ThatAquarel/protovolt/hardware/mini/interface.kicad_sch

## KiCad design hardware/mini/interface.kicad_sch (2025-06-21)

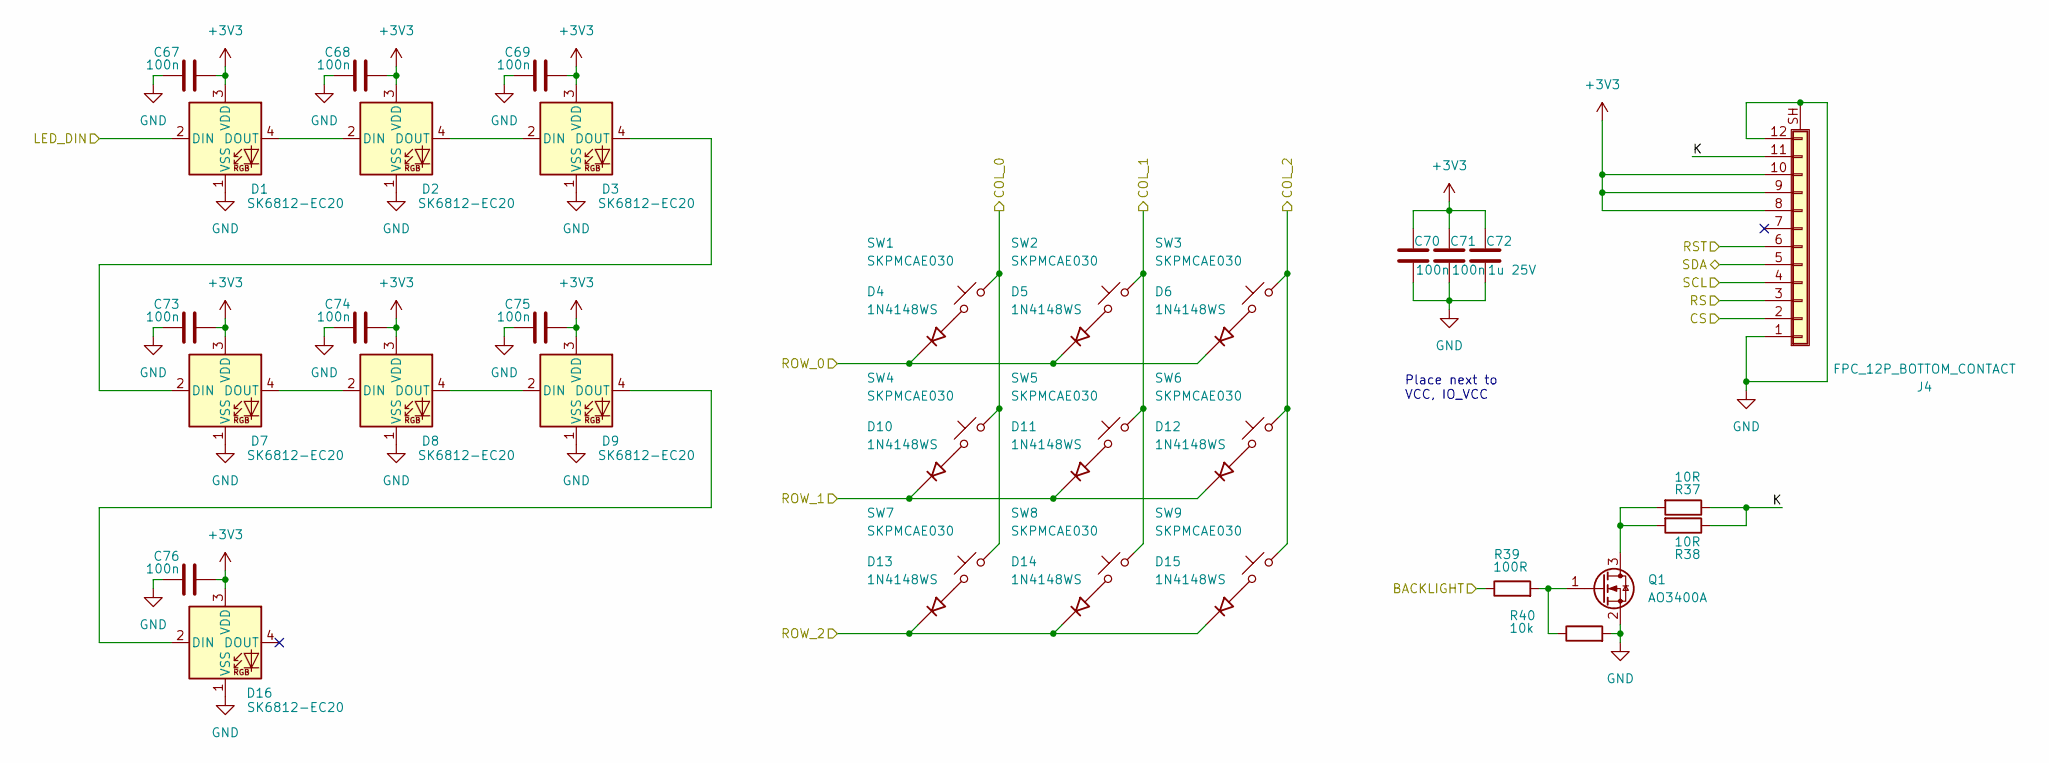
[picture p48: schematic interface.kicad_sch]

Parts:
C67, C68, C69, C70, C71, C73, C74, C75, C76: 100n; C_0402_1005Metric; LCSC C307331
C72: 1u 25V; C_0402_1005Metric; LCSC C52923
D1, D2, D3, D7, D8, D9, D16: SK6812-EC20; LED_SK6812_EC20_2.0x2.0mm; LCSC C2909058
D4, D5, D6, D10, D11, D12, D13, D14, D15: 1N4148WS; D_SOD-323; LCSC C2128
J4: FPC_12P_BOTTOM_CONTACT; JUSHUO_AFC07-S12ECA-00_1x12-1MP_P0.5mm_Horizontal; LCSC C262559
Q1: AO3400A; SOT-23-3; LCSC C20917
R37, R38: 10R; R_0402_1005Metric; LCSC C25077
R39: 100R; R_0402_1005Metric; LCSC C25076
R40: 10k; R_0402_1005Metric; LCSC C25744
SW1, SW2, SW3, SW4, SW5, SW6, SW7, SW8, SW9: SKPMCAE030; SW_PUSH_SKPM_6x5mm; LCSC C7430178

Connections:
+3V3: C67.2, C68.2, C69.2, C70.1, C71.1, C72.1, C73.2, C74.2, C75.2, C76.2, D1.3 (VDD), D2.3 (VDD), D3.3 (VDD), D7.3 (VDD), D8.3 (VDD), D9.3 (VDD), D16.3 (VDD), J4.8, J4.9, J4.10
BACKLIGHT: R39.1
COL_0: SW1.2, SW4.2, SW7.2
COL_1: SW2.2, SW5.2, SW8.2
COL_2: SW3.2, SW6.2, SW9.2
CS: J4.2
GND: C67.1, C68.1, C69.1, C70.2, C71.2, C72.2, C73.1, C74.1, C75.1, C76.1, D1.1 (VSS), D2.1 (VSS), D3.1 (VSS), D7.1 (VSS), D8.1 (VSS), D9.1 (VSS), D16.1 (VSS), J4.1, J4.12, J4.SH (Shield), Q1.2 (S), R40.2
K: J4.11, R37.1, R38.1
LED_DIN: D1.2 (DIN)
unnamed: D1.4 (DOUT), D2.2 (DIN)
unnamed: D2.4 (DOUT), D3.2 (DIN)
unnamed: D3.4 (DOUT), D7.2 (DIN)
unnamed: D4.2 (A), SW1.1
unnamed: D5.2 (A), SW2.1
unnamed: D6.2 (A), SW3.1
unnamed: D7.4 (DOUT), D8.2 (DIN)
unnamed: D8.4 (DOUT), D9.2 (DIN)
unnamed: D10.2 (A), SW4.1
unnamed: D11.2 (A), SW5.1
unnamed: D12.2 (A), SW6.1
unnamed: D13.2 (A), SW7.1
unnamed: D14.2 (A), SW8.1
unnamed: D15.2 (A), SW9.1
unnamed: D9.4 (DOUT), D16.2 (DIN)
unnamed: Q1.1 (G), R39.2, R40.1
unnamed: Q1.3 (D), R37.2, R38.2
ROW_0: D4.1 (K), D5.1 (K), D6.1 (K)
ROW_1: D10.1 (K), D11.1 (K), D12.1 (K)
ROW_2: D13.1 (K), D14.1 (K), D15.1 (K)
RS: J4.3
RST: J4.6
SCL: J4.4
SDA: J4.5

Notes on the sheet:
Place next to VCC, IO_VCC
