ThatAquarel/protovolt/hardware/mini/mcu.kicad_sch

## KiCad design hardware/mini/mcu.kicad_sch (2025-06-21)

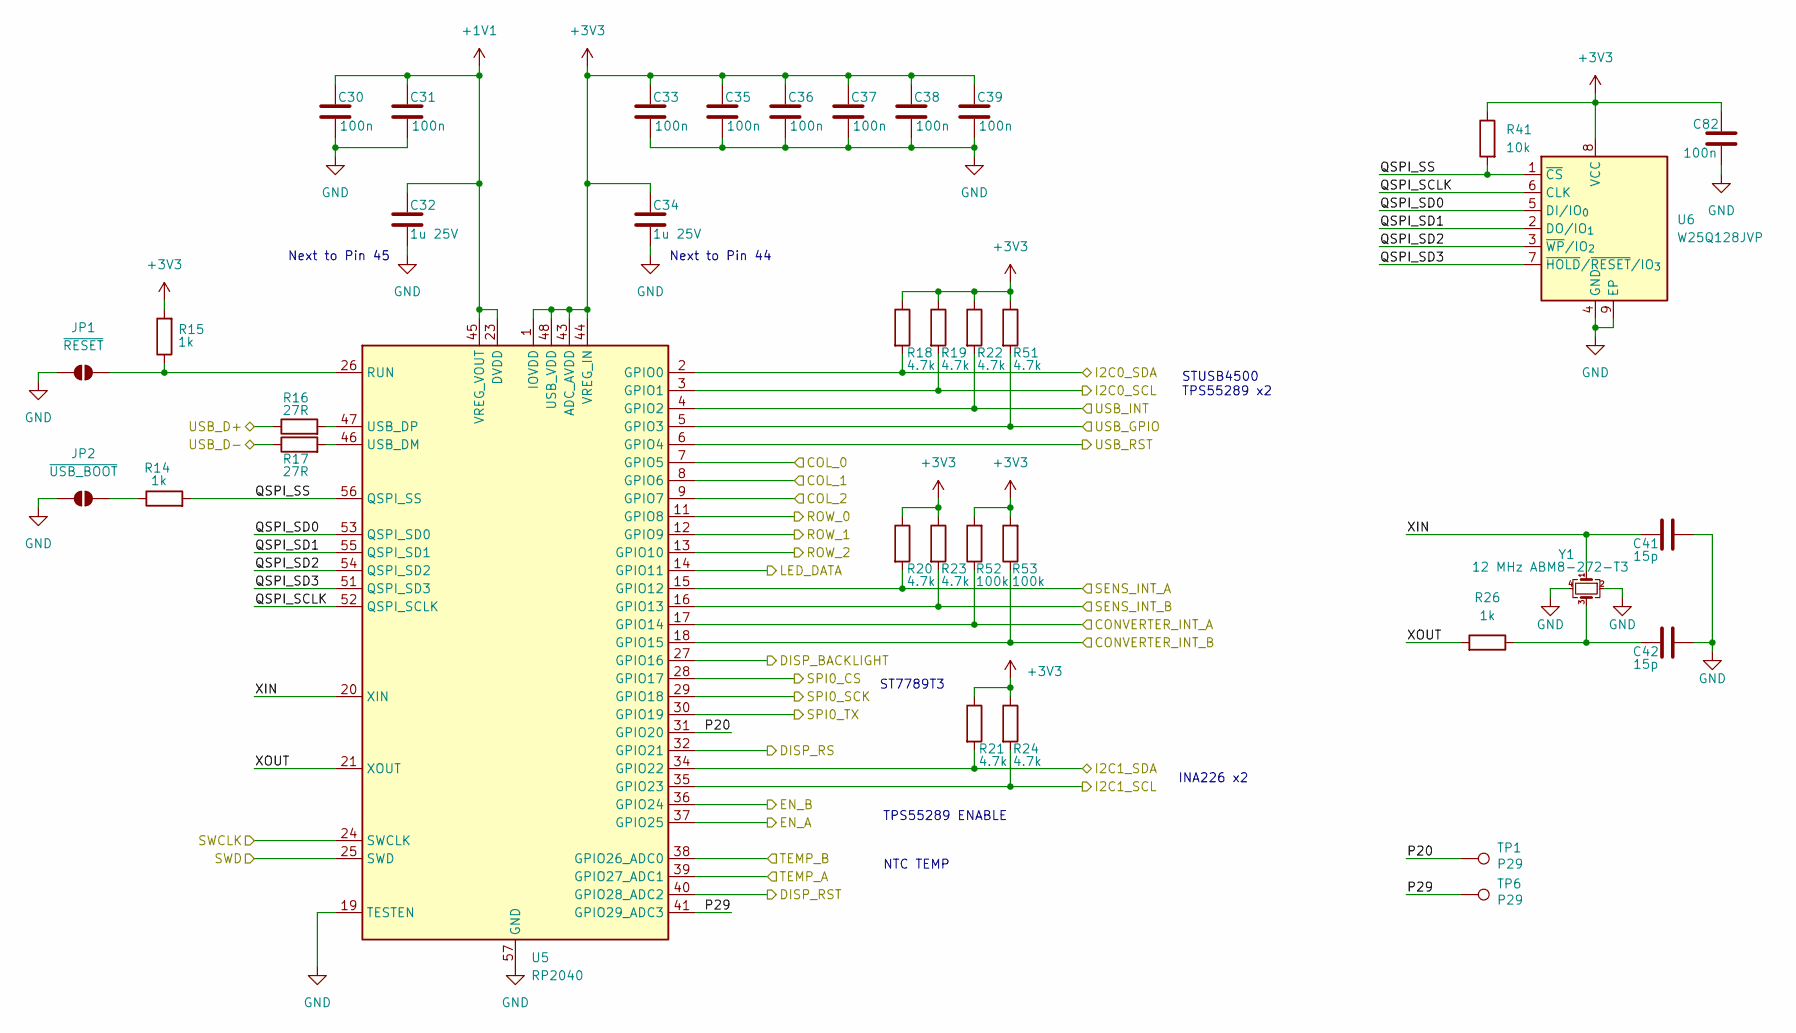
[picture p49: schematic mcu.kicad_sch]

Parts:
C30, C31, C33, C35, C36, C37, C38, C39, C82: 100n; C_0402_1005Metric; LCSC C307331
C32, C34: 1u 25V; C_0402_1005Metric; LCSC C52923
C41, C42: 15p; C_0402_1005Metric; LCSC C1548
JP1: ~{RESET}; SolderJumper-2_P1.3mm_Open_RoundedPad1.0x1.5mm
JP2: ~{USB_BOOT}; SolderJumper-2_P1.3mm_Open_RoundedPad1.0x1.5mm
R14, R15, R26: 1k; R_0402_1005Metric; LCSC C11702
R16, R17: 27R; R_0402_1005Metric; LCSC C138021
R18, R19, R20, R21, R22, R23, R24, R51: 4.7k; R_0402_1005Metric; LCSC C25900
R41: 10k; R_0402_1005Metric; LCSC C25744
R52, R53: 100k; R_0402_1005Metric; LCSC C25741
TP1, TP6: P29; TestPoint_Pad_D1.0mm
U5: RP2040; QFN-56-1EP_7x7mm_P0.4mm_EP3.2x3.2mm; LCSC C2040
U6: W25Q128JVP; WSON-8-1EP_6x5mm_P1.27mm_EP3.4x4.3mm; LCSC C190862
Y1: 12 MHz ABM8-272-T3; Crystal_SMD_Abracon_ABM8AIG-4Pin_3.2x2.5mm; LCSC C20625731

Connections:
+1V1: C30.1, C31.1, C32.1, U5.23 (DVDD), U5.45 (VREG_VOUT), U5.50 (DVDD)
+3V3: C33.1, C34.1, C35.1, C36.1, C37.1, C38.1, C39.1, C82.1, R15.2, R18.1, R19.1, R20.1, R21.1, R22.1, R23.1, R24.1, R41.1, R51.1, R52.2, R53.2, U5.1 (IOVDD), U5.10 (IOVDD), U5.22 (IOVDD), U5.33 (IOVDD), U5.42 (IOVDD), U5.43 (ADC_AVDD), U5.44 (VREG_IN), U5.48 (USB_VDD), U5.49 (IOVDD), U6.8 (VCC)
COL_0: U5.7 (GPIO5)
COL_1: U5.8 (GPIO6)
COL_2: U5.9 (GPIO7)
CONVERTER_INT_A: R52.1, U5.17 (GPIO14)
CONVERTER_INT_B: R53.1, U5.18 (GPIO15)
DISP_BACKLIGHT: U5.27 (GPIO16)
DISP_RS: U5.32 (GPIO21)
DISP_RST: U5.40 (GPIO28_ADC2)
EN_A: U5.37 (GPIO25)
EN_B: U5.36 (GPIO24)
GND: C30.2, C31.2, C32.2, C33.2, C34.2, C35.2, C36.2, C37.2, C38.2, C39.2, C41.1, C42.1, C82.2, JP1.1 (A), JP2.1 (A), U5.19 (TESTEN), U5.57 (GND), U6.4 (GND), U6.9 (EP), Y1.2, Y1.4
I2C0_SCL: R19.2, U5.3 (GPIO1)
I2C0_SDA: R18.2, U5.2 (GPIO0)
I2C1_SCL: R24.2, U5.35 (GPIO23)
I2C1_SDA: R21.2, U5.34 (GPIO22)
LED_DATA: U5.14 (GPIO11)
unnamed: C42.2, R26.1, Y1.3
unnamed: JP1.2 (B), R15.1, U5.26 (RUN)
unnamed: JP2.2 (B), R14.1
unnamed: R16.2, U5.47 (USB_DP)
unnamed: R17.2, U5.46 (USB_DM)
P20: TP1.1, U5.31 (GPIO20)
P29: TP6.1, U5.41 (GPIO29_ADC3)
QSPI_SCLK: U5.52 (QSPI_SCLK), U6.6 (CLK)
QSPI_SD0: U5.53 (QSPI_SD0), U6.5 (DI/IO_{0})
QSPI_SD1: U5.55 (QSPI_SD1), U6.2 (DO/IO_{1})
QSPI_SD2: U5.54 (QSPI_SD2), U6.3 (~WP/IO_{2})
QSPI_SD3: U5.51 (QSPI_SD3), U6.7 (~HOLD/~RESET/IO_{3})
QSPI_SS: R14.2, R41.2, U5.56 (QSPI_SS), U6.1 (~CS)
ROW_0: U5.11 (GPIO8)
ROW_1: U5.12 (GPIO9)
ROW_2: U5.13 (GPIO10)
SENS_INT_A: R20.2, U5.15 (GPIO12)
SENS_INT_B: R23.2, U5.16 (GPIO13)
SPI0_CS: U5.28 (GPIO17)
SPI0_SCK: U5.29 (GPIO18)
SPI0_TX: U5.30 (GPIO19)
SWCLK: U5.24 (SWCLK)
SWD: U5.25 (SWD)
TEMP_A: U5.39 (GPIO27_ADC1)
TEMP_B: U5.38 (GPIO26_ADC0)
USB_D+: R16.1
USB_D-: R17.1
USB_GPIO: R51.2, U5.5 (GPIO3)
USB_INT: R22.2, U5.4 (GPIO2)
USB_RST: U5.6 (GPIO4)
XIN: C41.2, U5.20 (XIN), Y1.1
XOUT: R26.2, U5.21 (XOUT)

Notes on the sheet:
TPS55289 ENABLE
INA226 x2
ST7789T3
Next to Pin 44
STUSB4500 TPS55289 x2
Next to Pin 45
NTC TEMP
