ThatAquarel/protovolt/hardware/mini/mini.kicad_sch

## KiCad design hardware/mini/mini.kicad_sch (2025-06-16)

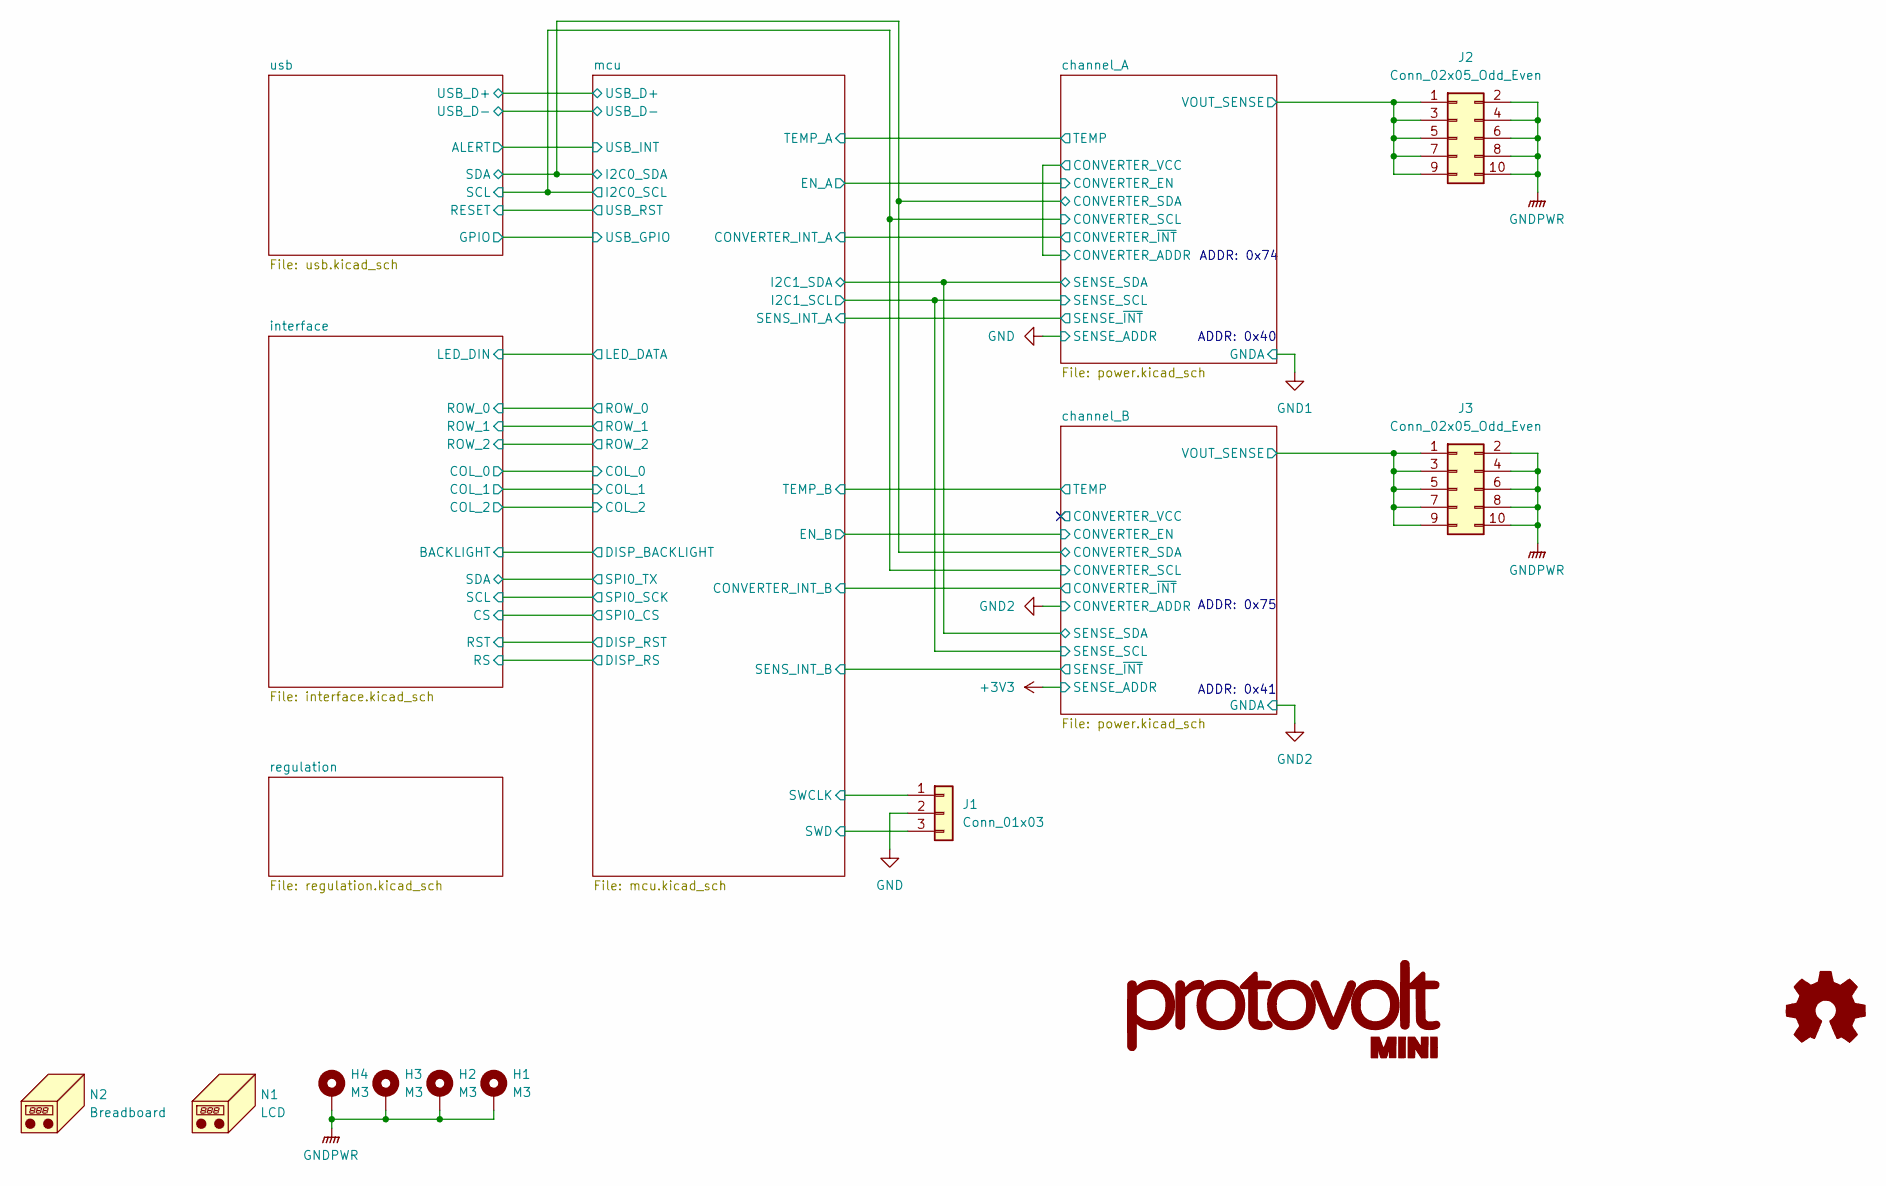
[picture p50: schematic mini.kicad_sch]

Parts:
H1, H2, H3, H4: M3; MountingHole_3.2mm_M3_DIN965_Pad_TopBottom
J1: Conn_01x03; SolderJumper-3_P1.3mm_Open_RoundedPad1.0x1.5mm
J2, J3: Conn_02x05_Odd_Even; PinHeader_2x05_P2.54mm_Vertical_SMD; LCSC C124391
N1: LCD; HS20HS072RX
N2: Breadboard; Breadboard_400P

Connections:
GND: J1.2
GNDPWR: H1.1, H2.1, H3.1, H4.1, J2.2, J2.4, J2.6, J2.8, J2.10, J3.2, J3.4, J3.6, J3.8, J3.10
SWCLK: J1.1
SWD: J1.3
VOUT_SENSE: J2.1, J2.3, J2.5, J2.7, J2.9, J3.1, J3.3, J3.5, J3.7, J3.9

Notes on the sheet:
ADDR: 0x41
ADDR: 0x40
ADDR: 0x74
ADDR: 0x75
