ThatAquarel/protovolt/hardware/mini/power.kicad_sch

## KiCad design hardware/mini/power.kicad_sch (2025-06-21)

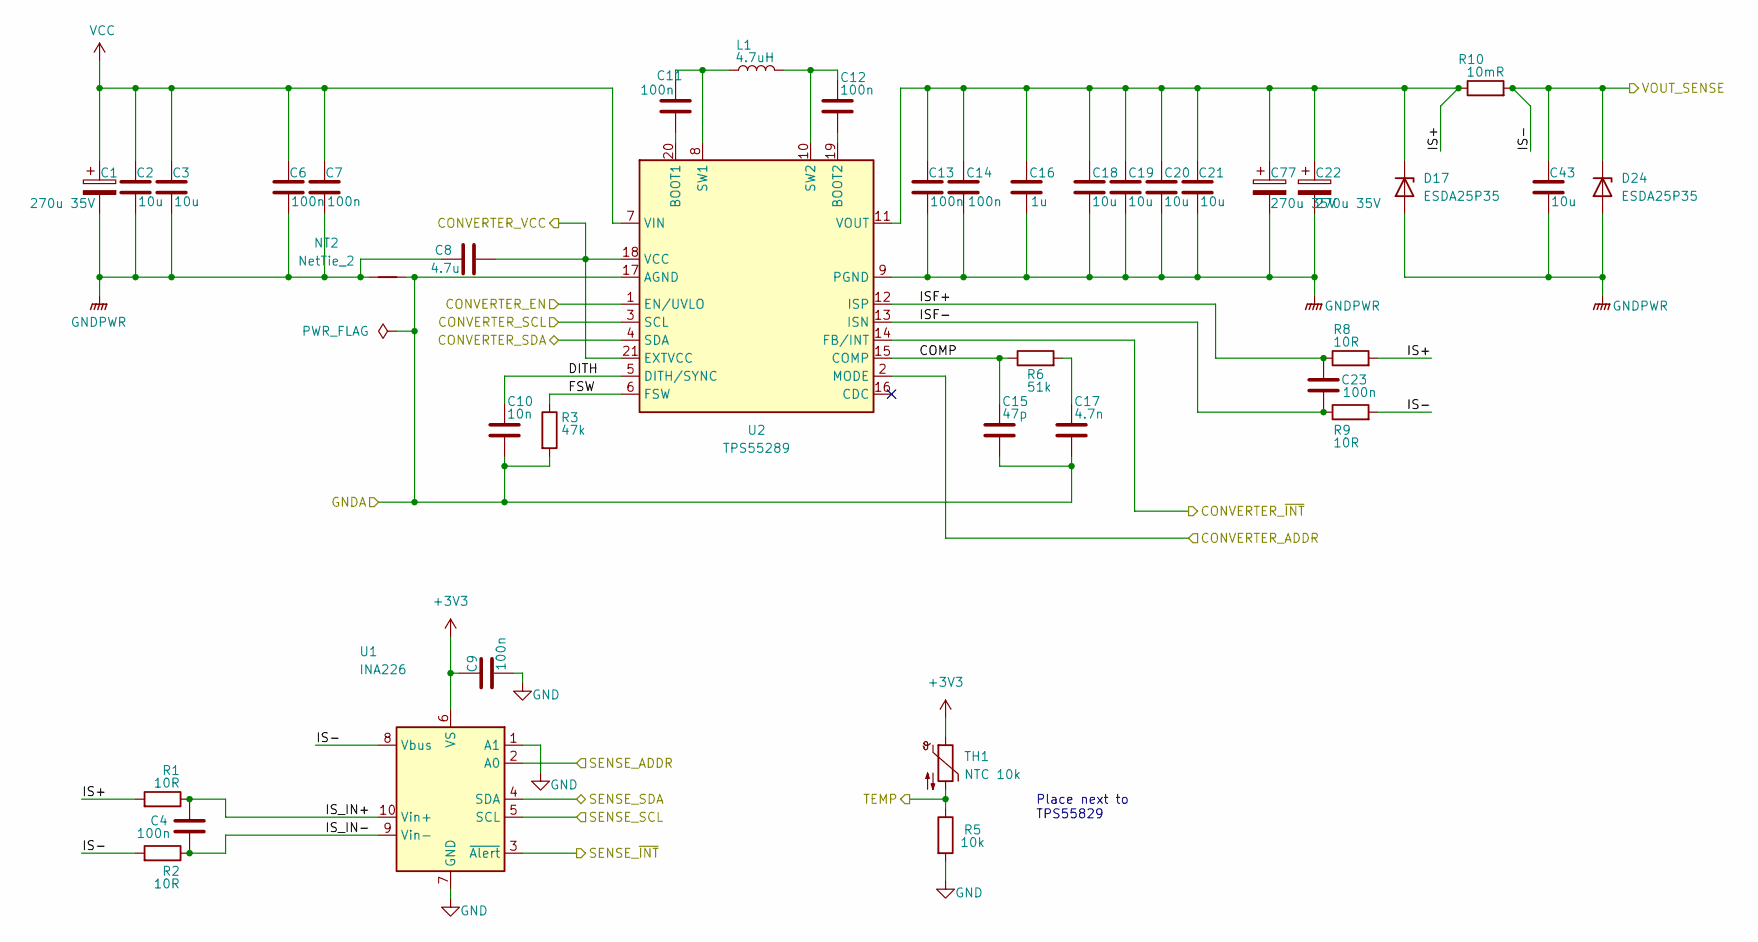
[picture p51: schematic power.kicad_sch]

Parts:
C1, C22, C77: 270u 35V; CP_Elec_10x10; LCSC C5246557
C2, C3, C18, C19, C20, C21, C43: 10u; C_1206_3216Metric; LCSC C13585
C4, C6, C7, C9, C11, C12, C13, C14, C23: 100n; C_0402_1005Metric; LCSC C307331
C8: 4.7u; C_0805_2012Metric; LCSC C1779
C10: 10n; C_0402_1005Metric; LCSC C15195
C15: 47p; C_0402_1005Metric; LCSC C1567
C16: 1u; C_1206_3216Metric; LCSC C1848
C17: 4.7n; C_0402_1005Metric; LCSC C1538
D17, D24: ESDA25P35; D_1610_4027Metric; LCSC C1974707
L1: 4.7uH; L_SOREDE_SRTC.1010; LCSC C7427509
NT2: NetTie_2; NetTie-2_SMD_Pad0.5mm
R1, R2, R8, R9: 10R; R_0402_1005Metric; LCSC C25077
R3: 47k; R_0402_1005Metric; LCSC C25792
R5: 10k; R_0402_1005Metric; LCSC C25744
R6: 51k; R_0402_1005Metric; LCSC C25794
R10: 10mR; R_0612_1632Metric; LCSC C21261108
TH1: NTC 10k; R_0402_1005Metric; LCSC C209959
U1: INA226; VSSOP-10_3x3mm_P0.5mm; LCSC C49851
U2: TPS55289; Texas_RYQ0021A_VQFN-21-1EP_5x3mm_P0.5mm; LCSC C5942077

Connections:
+3V3: C9.1, TH1.1, U1.6 (VS)
COMP: C15.1, R6.1, U2.15 (COMP)
CONVERTER_ADDR: U2.2 (MODE)
CONVERTER_EN: U2.1 (EN/UVLO)
CONVERTER_SCL: U2.3 (SCL)
CONVERTER_SDA: U2.4 (SDA)
CONVERTER_VCC: C8.1, U2.18 (VCC), U2.21 (EXTVCC)
CONVERTER_~INT: U2.14 (FB/INT)
DITH: C10.1, U2.5 (DITH/SYNC)
FSW: R3.1, U2.6 (FSW)
GND: C9.2, R5.2, U1.1 (A1), U1.7 (GND)
GNDA: C10.2, C15.2, C17.2, NT2.2, R3.2, U2.17 (AGND)
GNDPWR: C1.2, C2.2, C3.2, C6.2, C7.2, C8.2, C13.2, C14.2, C16.2, C18.2, C19.2, C20.2, C21.2, C22.2, C43.2, C77.2, D17.2 (A), D24.2 (A), NT2.1, U2.9 (PGND)
IS+: C13.1, C14.1, C16.1, C18.1, C19.1, C20.1, C21.1, C22.1, C77.1, D17.1 (K), R1.2, R8.2, R10.1, U2.11 (VOUT)
IS-: C43.1, D24.1 (K), R2.2, R9.2, R10.2, U1.8 (Vbus)
ISF+: C23.2, R8.1, U2.12 (ISP)
ISF-: C23.1, R9.1, U2.13 (ISN)
IS_IN+: C4.2, R1.1, U1.10 (Vin+)
IS_IN-: C4.1, R2.1, U1.9 (Vin-)
unnamed: C11.1, L1.1, U2.8 (SW1)
unnamed: C11.2, U2.20 (BOOT1)
unnamed: C12.1, L1.2, U2.10 (SW2)
unnamed: C12.2, U2.19 (BOOT2)
unnamed: C17.1, R6.2
SENSE_ADDR: U1.2 (A0)
SENSE_SCL: U1.5 (SCL)
SENSE_SDA: U1.4 (SDA)
SENSE_~INT: U1.3 (~Alert)
TEMP: R5.1, TH1.2
VCC: C1.1, C2.1, C3.1, C6.1, C7.1, U2.7 (VIN)

Notes on the sheet:
Place next to TPS55829
