ThatAquarel/protovolt/hardware/mini/regulation.kicad_sch

## KiCad design hardware/mini/regulation.kicad_sch (2025-06-21)

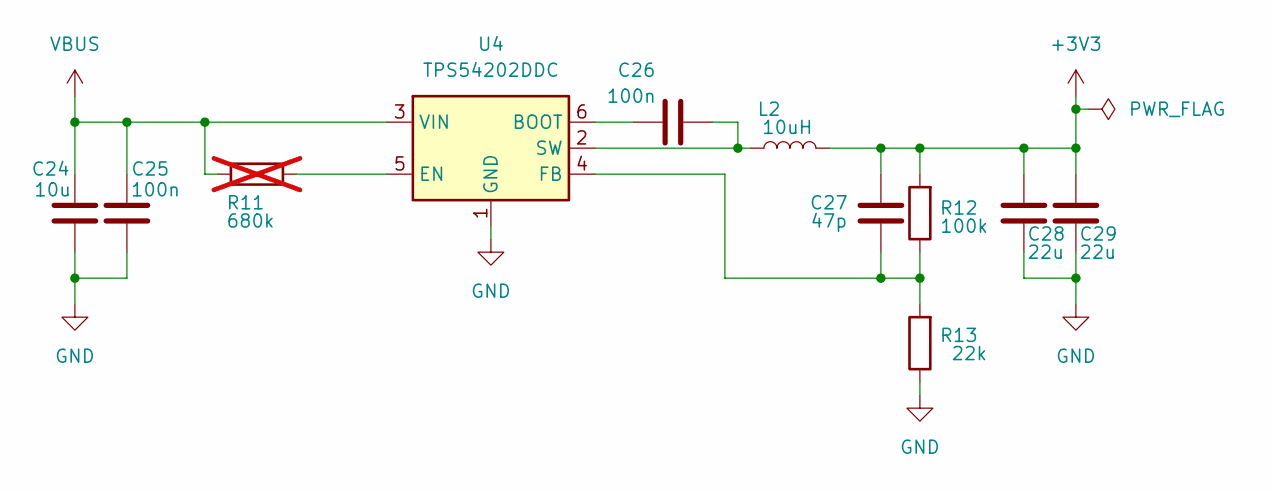
[picture p52: schematic regulation.kicad_sch]

Parts:
C24: 10u; C_1206_3216Metric; LCSC C13585
C25, C26: 100n; C_0402_1005Metric; LCSC C307331
C27: 47p; C_0402_1005Metric; LCSC C1567
C28, C29: 22u; C_0603_1608Metric; LCSC C59461
L2: 10uH; L_Changjiang_FXL0530; LCSC C177248
R11: 680k; R_0402_1005Metric; LCSC C4131; not fitted
R12: 100k; R_0402_1005Metric; LCSC C25741
R13: 22k; R_0402_1005Metric; LCSC C25768
U4: TPS54202DDC; SOT-23-6; LCSC C191884

Connections:
+3V3: C27.2, C28.2, C29.2, L2.2, R12.2
GND: C24.2, C25.1, C28.1, C29.1, R13.1, U4.1 (GND)
unnamed: C26.1, U4.6 (BOOT)
unnamed: C26.2, L2.1, U4.2 (SW)
unnamed: C27.1, R12.1, R13.2, U4.4 (FB)
unnamed: R11.1, U4.5 (EN)
VBUS: C24.1, C25.2, R11.2, U4.3 (VIN)
