ThatAquarel/protovolt/hardware/mini/temperature.kicad_sch

## KiCad design hardware/mini/temperature.kicad_sch (2025-06-09)

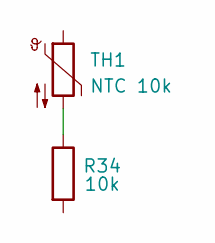
[picture p53: schematic temperature.kicad_sch]

Parts:
R34: 10k
TH1: NTC 10k

Connections:
unnamed: R34.1, TH1.2
