ThatAquarel/protovolt/hardware/mini/usb.kicad_sch

## KiCad design hardware/mini/usb.kicad_sch (2025-06-21)

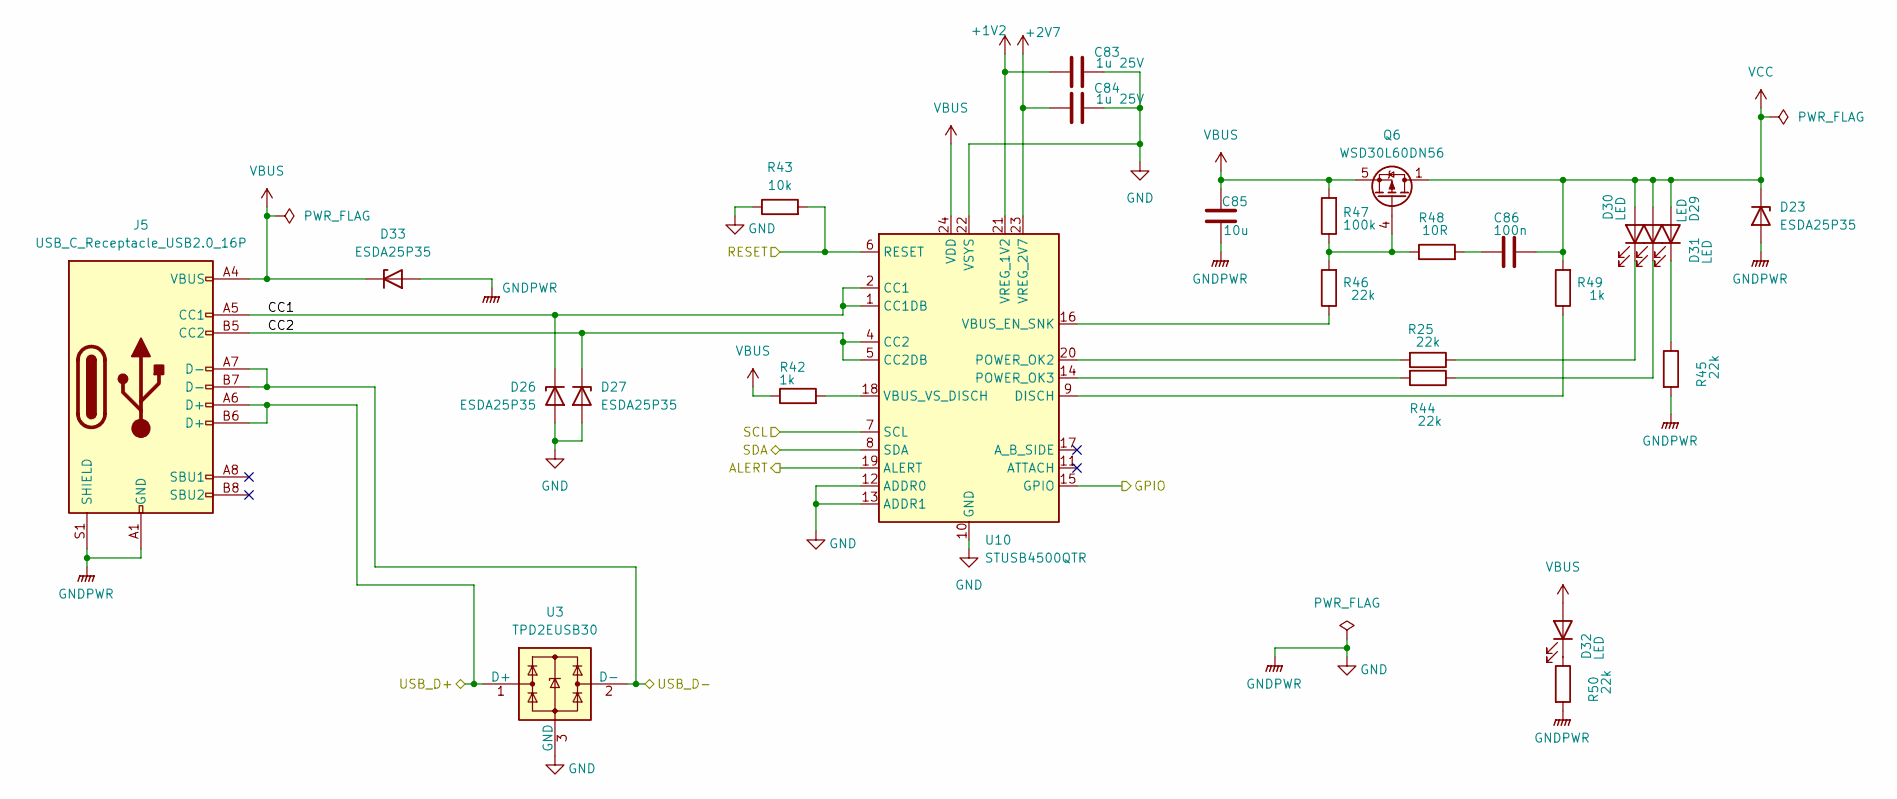
[picture p54: schematic usb.kicad_sch]

Parts:
C83, C84: 1u 25V; C_0402_1005Metric; LCSC C52923
C85: 10u; C_1206_3216Metric; LCSC C13585
C86: 100n; C_0402_1005Metric; LCSC C307331
D23, D26, D27, D33: ESDA25P35; D_1610_4027Metric; LCSC C1974707
D29, D30, D31, D32: LED; LED_0603_1608Metric; LCSC C2286
J5: USB_C_Receptacle_USB2.0_16P; USB_C_Receptacle_GCT_USB4105-xx-A_16P_TopMnt_Horizontal; LCSC C165948
Q6: WSD30L60DN56; PQFN-8-EP_6x5mm_P1.27mm_Generic; LCSC C148397
R25, R44, R45, R46, R50: 22k; R_0402_1005Metric; LCSC C25768
R42, R49: 1k; R_0402_1005Metric; LCSC C11702
R43: 10k; R_0402_1005Metric; LCSC C25744
R47: 100k; R_0402_1005Metric; LCSC C25741
R48: 10R; R_0402_1005Metric; LCSC C25077
U3: TPD2EUSB30; Texas_DRT-3; LCSC C97502
U10: STUSB4500QTR; QFN-24-1EP_4x4mm_P0.5mm_EP2.7x2.7mm; LCSC C2678061

Connections:
+1V2: C83.1, U10.21 (VREG_1V2)
+2V7: C84.1, U10.23 (VREG_2V7)
ALERT: U10.19 (ALERT)
CC1: D26.1 (K), J5.A5 (CC1), U10.1 (CC1DB), U10.2 (CC1)
CC2: D27.1 (K), J5.B5 (CC2), U10.4 (CC2), U10.5 (CC2DB)
GND: C83.2, C84.2, C85.2, D23.2 (A), D26.2 (A), D27.2 (A), D33.2 (A), J5.A1 (GND), J5.A12 (GND), J5.B1 (GND), J5.B12 (GND), J5.S1 (SHIELD), R43.1, R45.2, R50.2, U3.3 (GND), U10.10 (GND), U10.12 (ADDR0), U10.13 (ADDR1), U10.22 (VSYS), U10.25 (GND)
GPIO: U10.15 (GPIO)
unnamed: C86.2, R48.2
unnamed: D29.1 (K), R25.1
unnamed: D30.1 (K), R44.1
unnamed: D31.1 (K), R45.1
unnamed: D32.1 (K), R50.1
unnamed: Q6.4 (G), R46.2, R47.1, R48.1
unnamed: R25.2, U10.20 (POWER_OK2)
unnamed: R42.2, U10.18 (VBUS_VS_DISCH)
unnamed: R44.2, U10.14 (POWER_OK3)
unnamed: R46.1, U10.16 (VBUS_EN_SNK)
unnamed: R49.1, U10.9 (DISCH)
RESET: R43.2, U10.6 (RESET)
SCL: U10.7 (SCL)
SDA: U10.8 (SDA)
USB_D+: J5.A6 (D+), J5.B6 (D+), U3.1 (D+)
USB_D-: J5.A7 (D-), J5.B7 (D-), U3.2 (D-)
VBUS: C85.1, D32.2 (A), D33.1 (K), J5.A4 (VBUS), J5.A9 (VBUS), J5.B4 (VBUS), J5.B9 (VBUS), Q6.5 (S), R42.1, R47.2, U10.24 (VDD)
VCC: C86.1, D23.1 (K), D29.2 (A), D30.2 (A), D31.2 (A), Q6.1 (D), Q6.2 (D), Q6.3 (D), R49.2
