ThatAquarel/protovolt/protov-hal-mock/src/lib.rs

pub mod device;
pub mod dispatch;
pub mod pool;
pub mod scpi;
pub mod server;
pub mod state;
pub mod telemetry;
mod ws;

#[cfg(feature = "render-ui")]
pub mod render;

pub use device::MockDevice;
pub use pool::{DevicePool, MAX_MOCK_DEVICES, SLOT_PROFILES, SlotProfile};
pub use server::{MockServer, RunningServer, ServerConfig};
