ThatAquarel/protovolt/protov-core/src/scpi/parser.rs

pub use protov_scpi::{
    ChannelParam, FWUP_DATA_PREFIX, MeasKind, ScpiCommand, TempSlot, is_allowed_in_update_mode,
    is_mutation, normalize_command, parse_command, requires_active_update_session,
};

#[cfg(test)]
mod tests;
